j0ntan/CCNY-SG-Load/CCNY_Smart_Grid_Load/include/RelayStateGenerator.h

#ifndef RELAYSTATEGENERATOR
#define RELAYSTATEGENERATOR

class InputSequence;
class RelayState;

bool isValidSequence(const InputSequence& input);
void recordNewRelayState(const InputSequence& input, RelayState& relayState);

#endif  // RELAYSTATEGENERATOR
