j0ntan/CCNY-SG-Load/CCNY_Smart_Grid_Load/src/HardwareSDFlash.cpp

#include "../include/HardwareSDFlash.h"
#include "../include/HardwareTextFile.h"
#include <SD.h>  // includes an "extern SDClass SD"

extern "C" {
void pinMode(uint8_t, uint8_t);
}

HardwareSDFlash::HardwareSDFlash(uint8_t chipSelectPin)
    : chip_select(chipSelectPin) {}

HardwareSDFlash::~HardwareSDFlash() { SD.end(); }

bool HardwareSDFlash::connected() const {
  pinMode(chip_select, 0x1 /*OUTPUT mode*/);
  return SD.begin(chip_select);
}

bool HardwareSDFlash::fileExists(const char* filename) const {
  return SD.exists(filename);
}

TextFile* HardwareSDFlash::openFile(const char* filename) const {
  return new HardwareTextFile{SD.open(filename)};
}
