j0ntan/CCNY-SG-Load/CCNY_Smart_Grid_Load/src/HardwareTimer.cpp

#include "../include/HardwareTimer.h"
#include <Arduino.h>

void HardwareTimer::delay(Timer::milliseconds ms) const { ::delay(ms); }

void HardwareTimer::delayMicroseconds(Timer::microseconds us) const {
  ::delayMicroseconds(us);
}
