j0ntan/CCNY-SG-Load/CCNY_Smart_Grid_Load/include/InputSequence.h

#ifndef INPUTSEQUENCE_H
#define INPUTSEQUENCE_H

#include <stdint.h>

class InputSequence {
 public:
  InputSequence() = default;
  ~InputSequence() = default;

  InputSequence(const InputSequence& seq);
  InputSequence& operator=(const InputSequence& rhs);

  uint8_t length() const;

  char& operator[](uint8_t index);
  char operator[](uint8_t index) const;

  void applyBalancedSequence(uint8_t amount);
  void applyResetSequence();
  void cancelSequence();

  void addInput(char input);
  void addInput(const char* input_str);
  void removeLastInput();

  static const uint8_t SIZE = 12;  // 11 chars + null terminator

 private:
  char buffer[SIZE] = {};
};

#endif  // INPUTSEQUENCE_H
