j0ntan/CCNY-SG-Load/CCNY_Smart_Grid_Load/include/ShiftRegister.h

#ifndef SHIFT_REGISTER_H
#define SHIFT_REGISTER_H

#include <stdint.h>

class DigitalOutput;

class ShiftRegister {
 public:
  typedef uint8_t byte;

  ShiftRegister(const DigitalOutput *serialDataInput,
                const DigitalOutput *shiftRegisterClock,
                const DigitalOutput *storageRegisterClock);

  ShiftRegister() = delete;
  ShiftRegister(const ShiftRegister &) = delete;
  ShiftRegister &operator=(const ShiftRegister &rhs) = delete;

  void shiftByte(const byte &data) const;
  void updateOutput() const;
  void outputByte(const byte &data) const;

 private:
  void _initPins() const;
  void _initOutputs() const;
  void _ticShiftRegisterClock() const;
  void _ticStorageRegisterClock() const;

  // outputs to shift register
  const DigitalOutput *_SERIAL_DATA_INPUT;
  const DigitalOutput *_SHIFT_REGISTER_CLOCK;
  const DigitalOutput *_STORAGE_REGISTER_CLOCK;

  // clock periods in microseconds
  static const unsigned int _SHIFT_CLOCK_DELAY = 1000;
  static const unsigned int _STORAGE_CLOCK_DELAY = 1000;
};

#endif  // SHIFT_REGISTER_H
