j0ntan/CCNY-SG-Load/CCNY_Smart_Grid_Load/include/Timer.h

#ifndef TIMER_H
#define TIMER_H

class Timer {
 public:
  typedef unsigned long milliseconds;
  typedef unsigned long microseconds;

  virtual ~Timer() = default;

  virtual void delay(milliseconds) const = 0;
  virtual void delayMicroseconds(microseconds) const = 0;
};

#endif  // TIMER_H
